Wogambula/Popsicle-Stick-Bridge-Competition/ALL/IMAGES/WhatsApp Image 2026-03-06 at 10.54.57 PM (2).jpeg

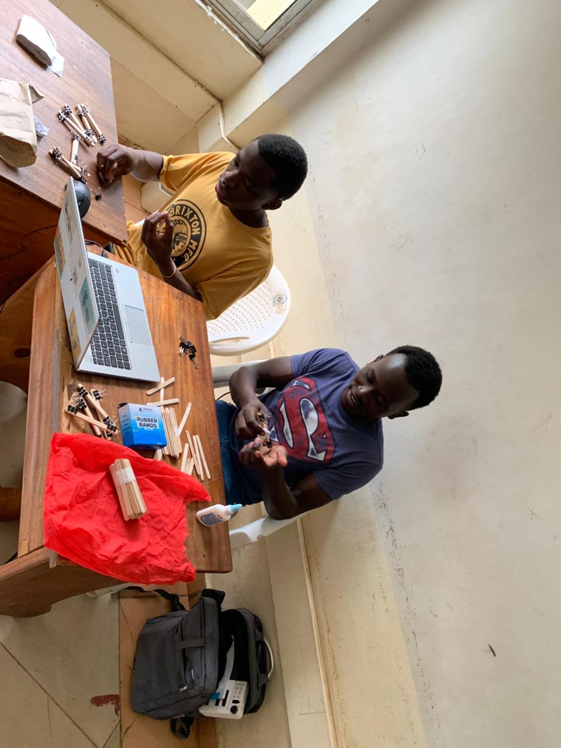
ALL/IMAGES/WhatsApp Image 2026-03-06 at 10.54.57 PM (2).jpeg
